radioation/Devastar/gun_camera/devastar_common.h

#ifndef _DEVASTAR_COMMON_H_
#define _DEVASTAR_COMMON_H_

namespace devastar {

  enum ButtonCodes
  {
    BUTTON_NONE = 0x00,
    BUTTON_A = 0x01,
    BUTTON_B = 0x02,
    BUTTON_C = 0x04,
    BUTTON_D = 0x08,
    BUTTON_E = 0x10 
  };

}

#endif // _DEVASTAR_COMMON_H_
